pkElectronics/STM32WB55_PlantSensor/Software/Src/app_fatfs.c

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

/* Includes ------------------------------------------------------------------*/
#include "app_fatfs.h"
#include "main.h"

/* USER CODE BEGIN PTD */
typedef enum {
  APPLICATION_IDLE = 0,
  APPLICATION_INIT,
  APPLICATION_RUNNING,
  APPLICATION_SD_UNPLUGGED,
}FS_FileOperationsTypeDef;
/* USER CODE END PTD */

FATFS USERFatFs;    /* File system object for USER logical drive */
FIL USERFile;       /* File  object for USER */
char USERPath[4];   /* USER logical drive path */
/* USER CODE BEGIN PV */
FS_FileOperationsTypeDef Appli_state = APPLICATION_IDLE;
/* USER CODE END PV */

/**
  * @brief  FatFs initialization
  * @param  None
  * @retval Initialization result 
  */
int32_t MX_FATFS_Init(void) 
{
  /*## FatFS: Link the disk I/O driver(s)  ###########################*/
  if (FATFS_LinkDriver(&USER_Driver, USERPath) != 0)
  /* USER CODE BEGIN FATFS_Init */
  {
    return APP_ERROR;
  }
  else
  {
    Appli_state = APPLICATION_INIT;
    return APP_OK;
  }
  /* USER CODE END FATFS_Init */
}

/**
  * @brief  FatFs application main process
  * @param  None
  * @retval Process result 
  */
int32_t MX_FATFS_Process(void)
{
  /* USER CODE BEGIN FATFS_Process */
  int32_t process_res = APP_OK;  
    
  return process_res;
  /* USER CODE END FATFS_Process */
}  

/**
  * @brief  Gets Time from RTC (generated when FS_NORTC==0; see ff.c)
  * @param  None
  * @retval Time in DWORD
  */
DWORD get_fattime(void)
{
  /* USER CODE BEGIN get_fattime */
  return 0;
  /* USER CODE END get_fattime */  
}

/************************ (C) COPYRIGHT STMicroelectronics *****END OF FILE****/
